slopy1/doa_24ghz_t/gnuradio_flowgraphs/aoa_estimation_bladerf.pdf

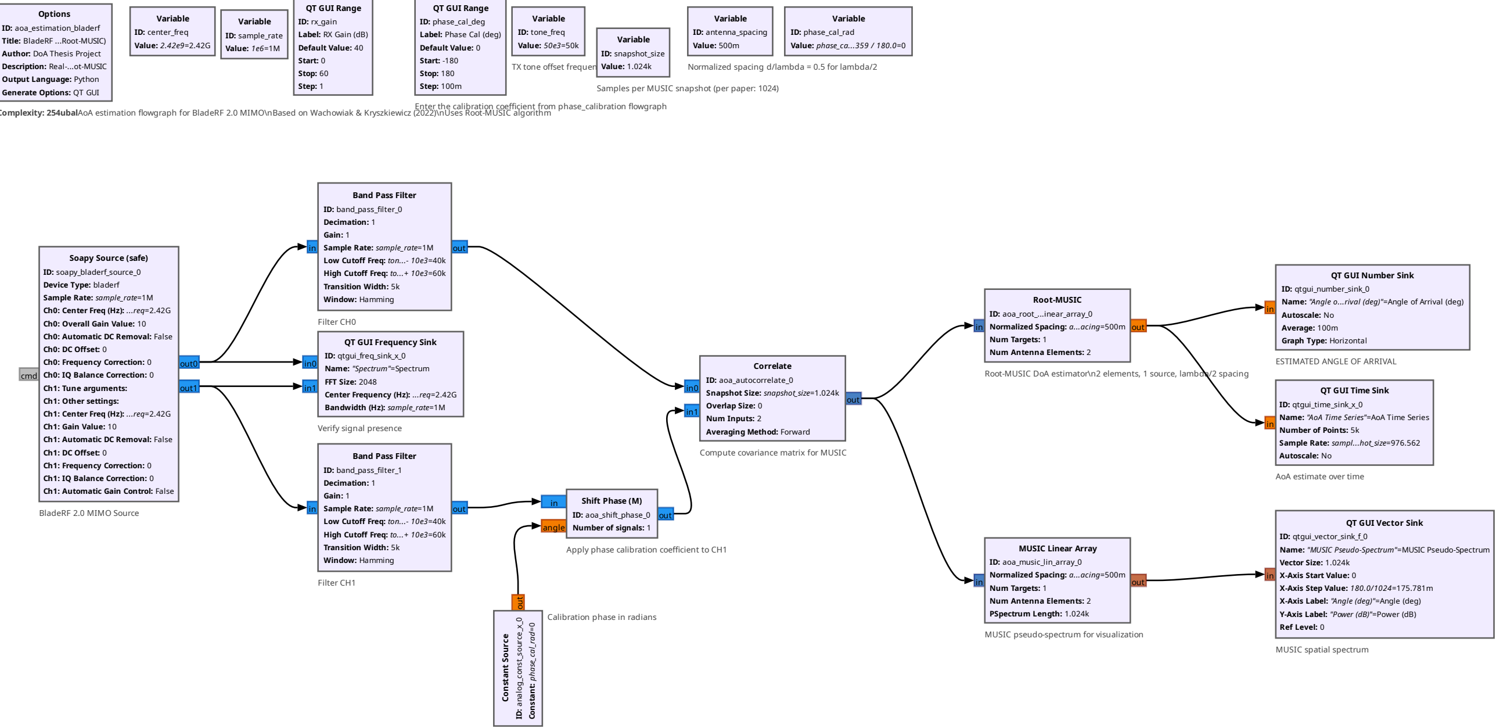
[picture p1: figure]
TX tone offset frequency; Calibration phase in radians; Compute covariance matrix for MUSIC; MUSIC pseudo-spectrum for visualization; Filter CH0; Filter CH1; Verify signal presence; ESTIMATED ANGLE OF ARRIVAL; AoA estimate over time; MUSIC spatial spectrum; BladeRF 2.0 MIMO Source; Options ID: aoa_estimation_bladerf Title: BladeRF ...Root-MUSIC) Author: DoA Thesis Project Description: Real-...ot-MUSIC Output Language: Python Generate Options: QT GUI; Variable ID: antenna_spacing Value: 500m; Variable ID: center_freq Value: 2.42e9=2.42G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

Complexity: 254ubalAoA estimation flowgraph for BladeRF 2.0 MIMO\nBased on Wachowiak & Kryszkiewicz (2022)\nUses Root-MUSIC algorithm

Normalized spacing d/lambda = 0.5 for lambda/2

Enter the calibration coefficient from phase_calibration flowgraph

Samples per MUSIC snapshot (per paper: 1024)

Root-MUSIC DoA estimator\n2 elements, 1 source, lambda/2 spacing

Apply phase calibration coefficient to CH1

Name: "Angle o...rival (deg)"=Angle of Arrival (deg)
