slopy1/doa_24ghz_t/results/spectrum_sweep_20260427_003050/spectrum_compare.png

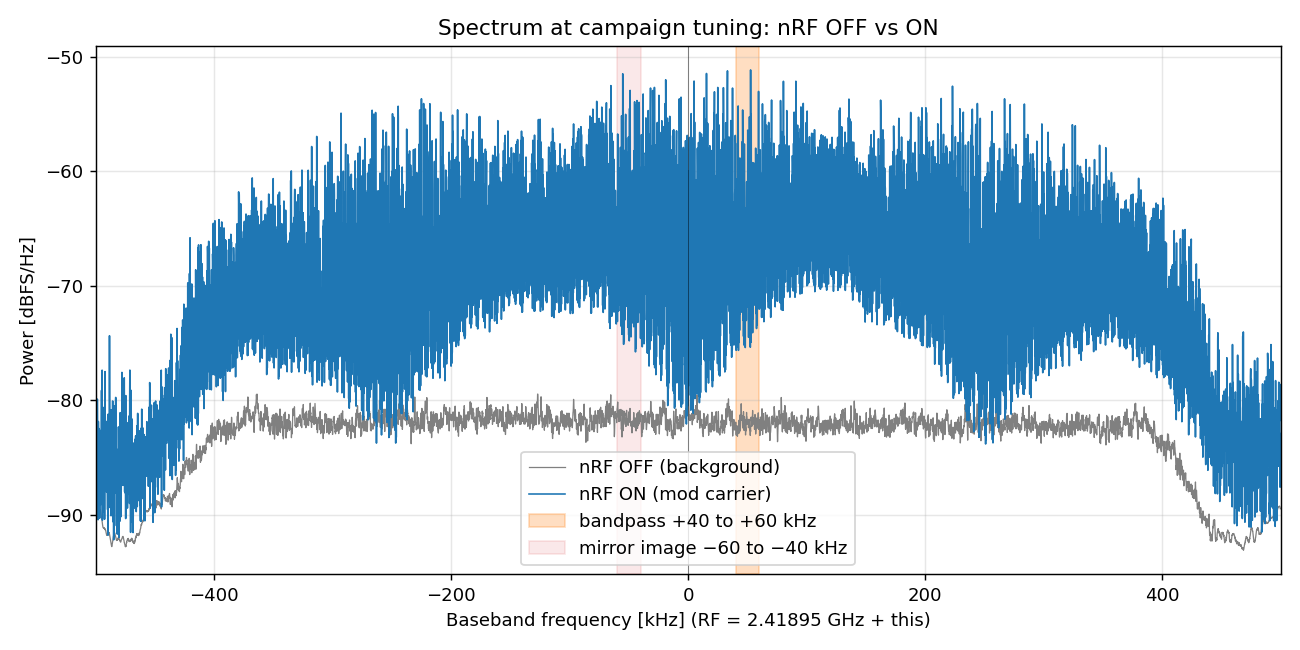
results/spectrum_sweep_20260427_003050/spectrum_compare.png
