slopy1/doa_24ghz_t/results/advisor_summary/arm_vs_fpga_delta.png

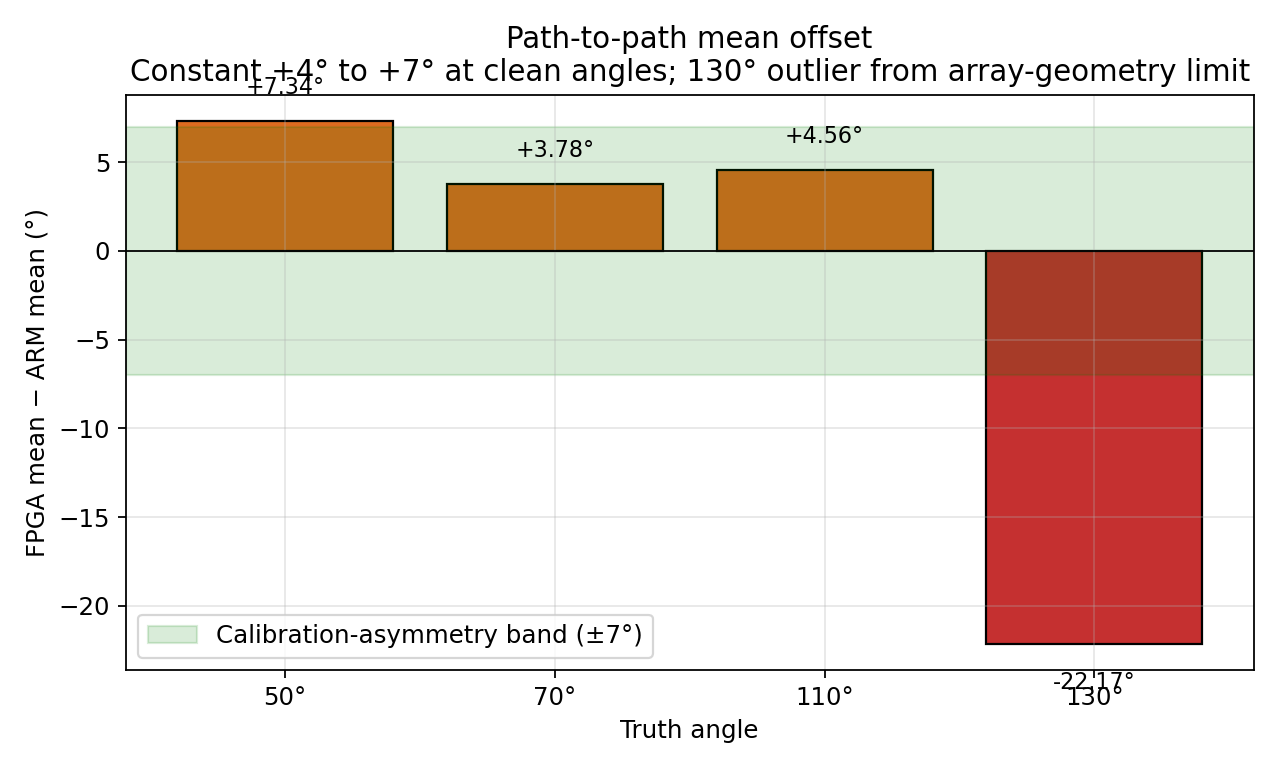
results/advisor_summary/arm_vs_fpga_delta.png
