slopy1/doa_24ghz_t/results/advisor_summary/arm_vs_fpga_per_angle.png

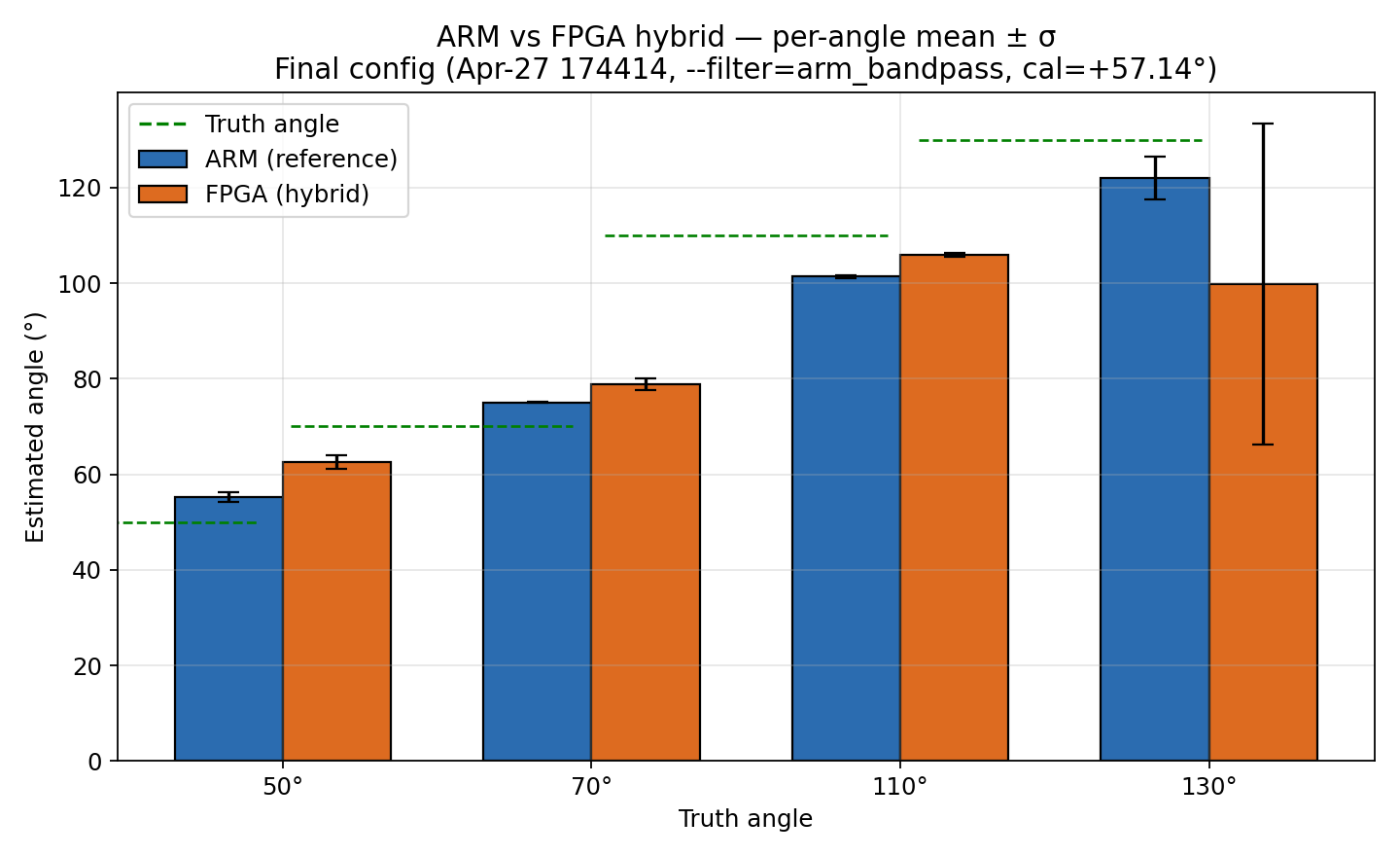
results/advisor_summary/arm_vs_fpga_per_angle.png
