slopy1/doa_24ghz_t/results/advisor_summary/broadside_anchor.png

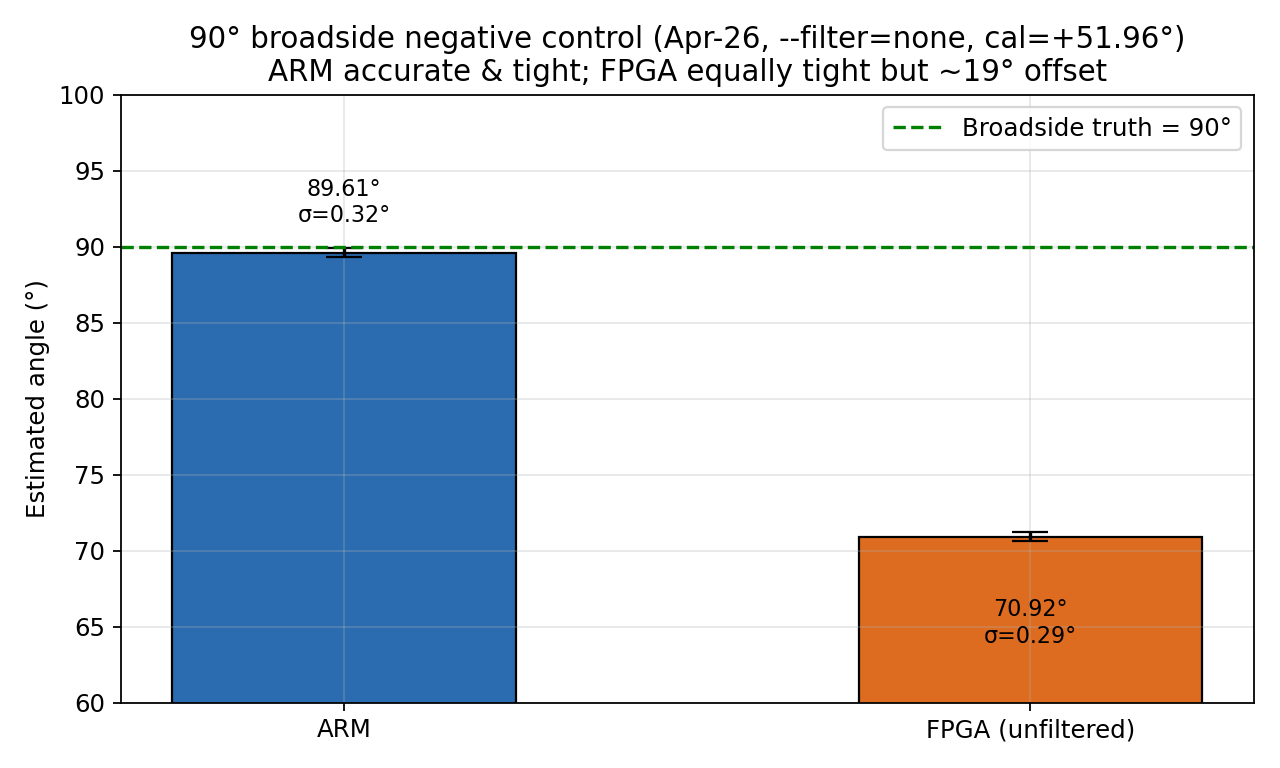
results/advisor_summary/broadside_anchor.png
