slopy1/doa_24ghz_t/results/advisor_summary/filter_regime_comparison.png

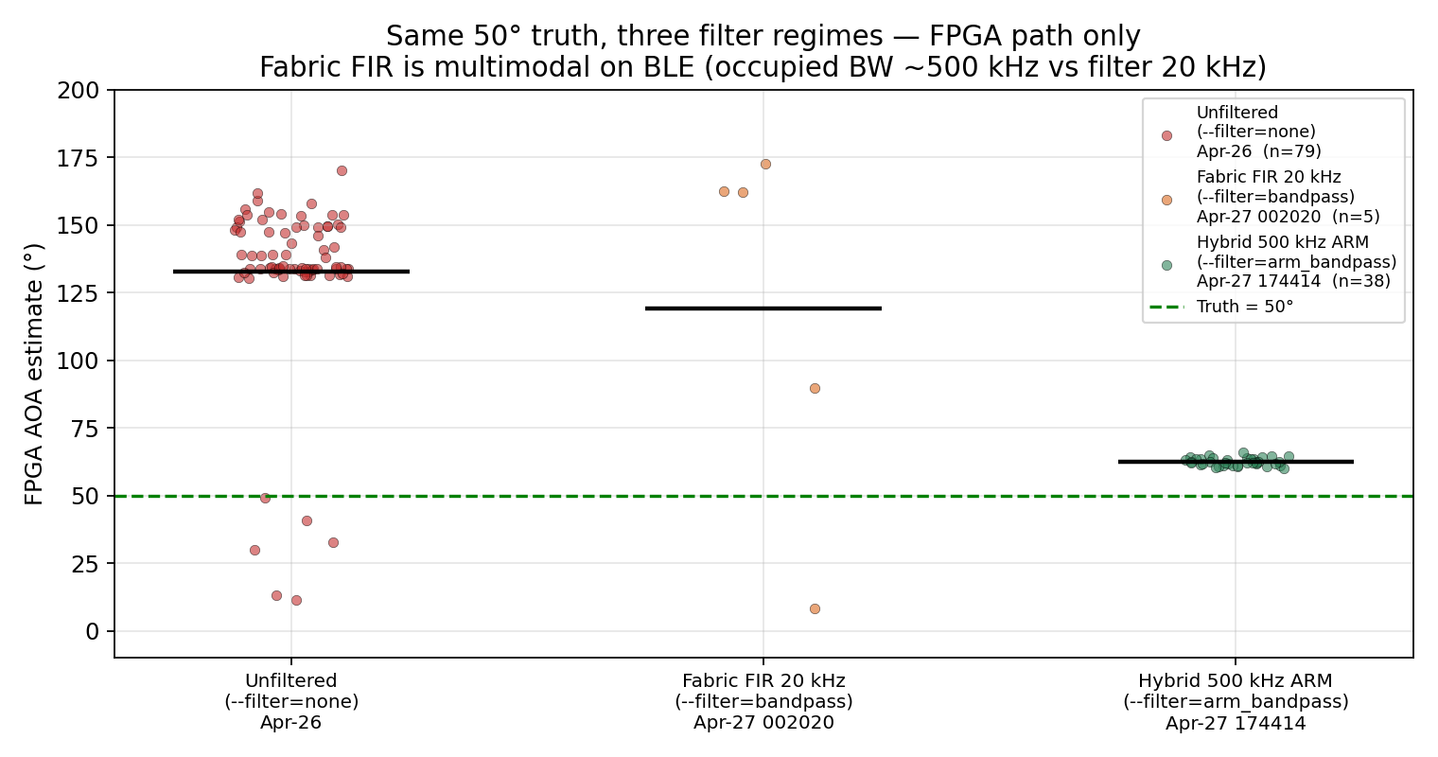
results/advisor_summary/filter_regime_comparison.png
