slopy1/doa_24ghz_t/results/advisor_summary/methodology_r2.png

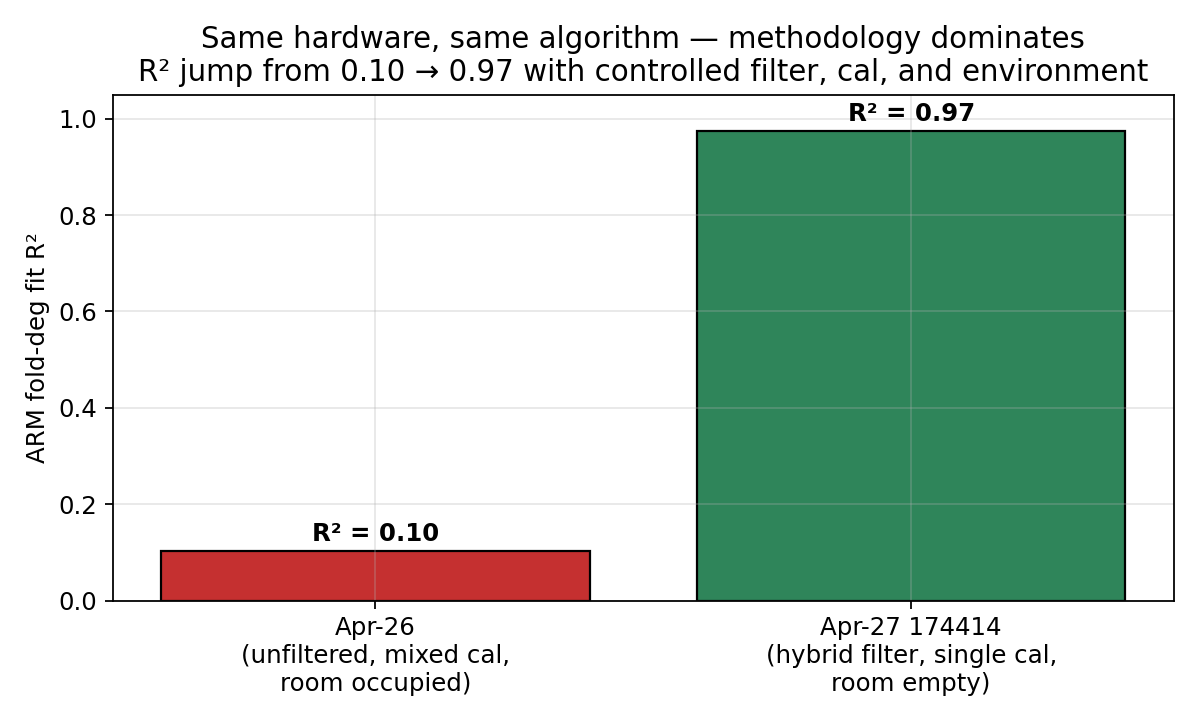
results/advisor_summary/methodology_r2.png
