slopy1/doa_24ghz_t/results/arm_vs_fpga/hist_rootmusic_pair_90deg.png

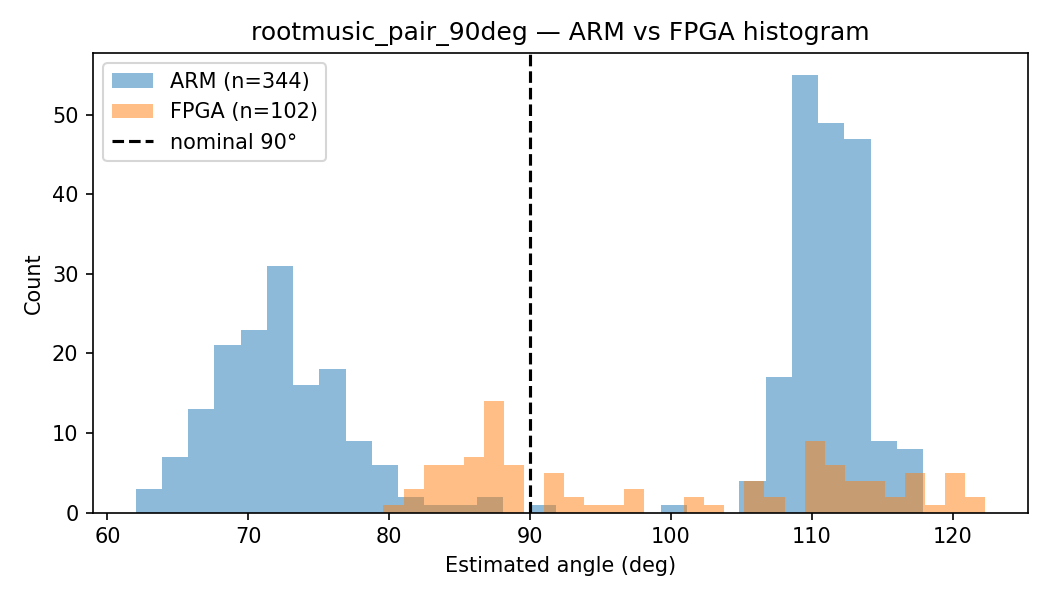
results/arm_vs_fpga/hist_rootmusic_pair_90deg.png
