slopy1/doa_24ghz_t/results/arm_vs_fpga/multi_algo_summary.png

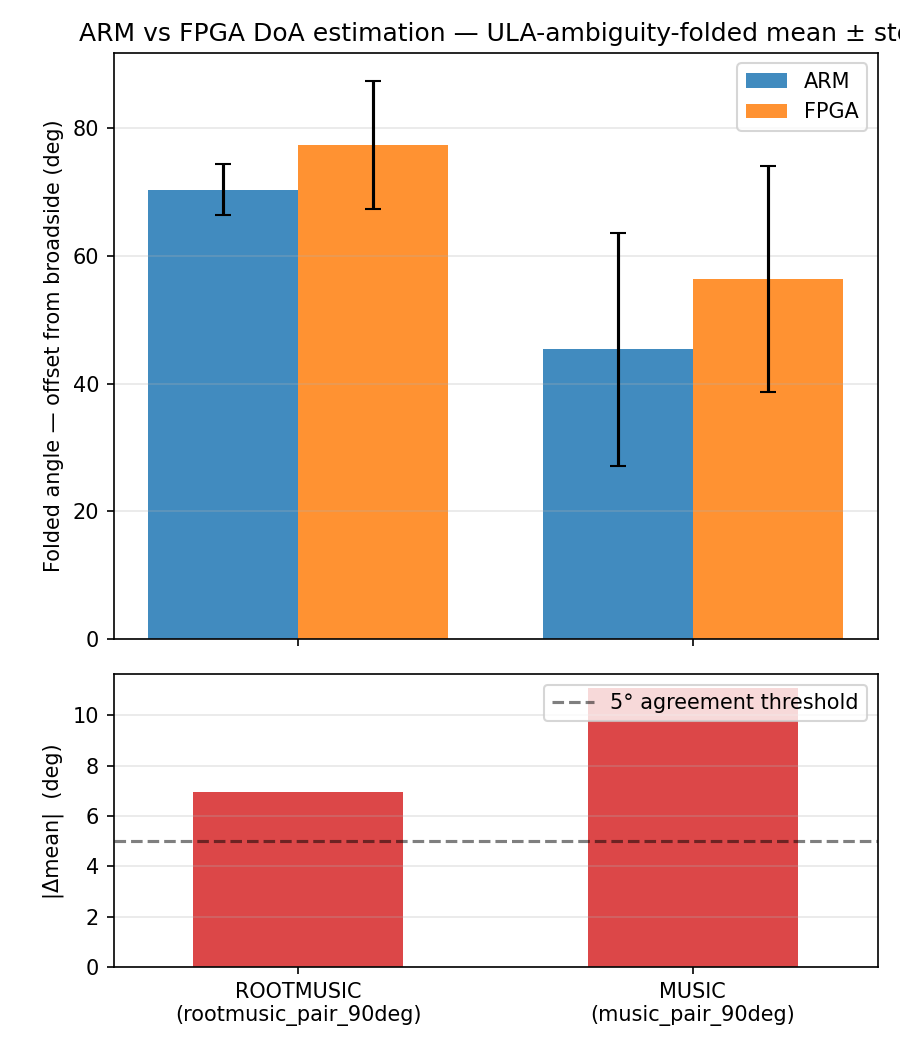
results/arm_vs_fpga/multi_algo_summary.png
