slopy1/doa_24ghz_t/results/arm_vs_fpga/timeseries_music_pair_90deg.png

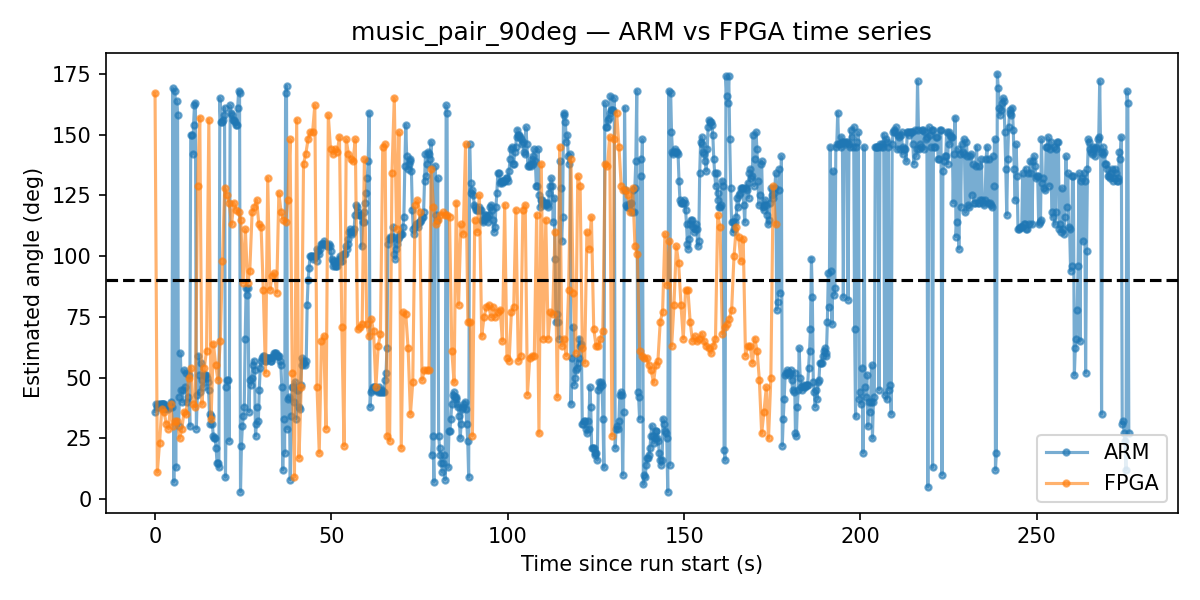
results/arm_vs_fpga/timeseries_music_pair_90deg.png
