slopy1/doa_24ghz_t/results/campaign_20260426/folded_measured_vs_truth.png

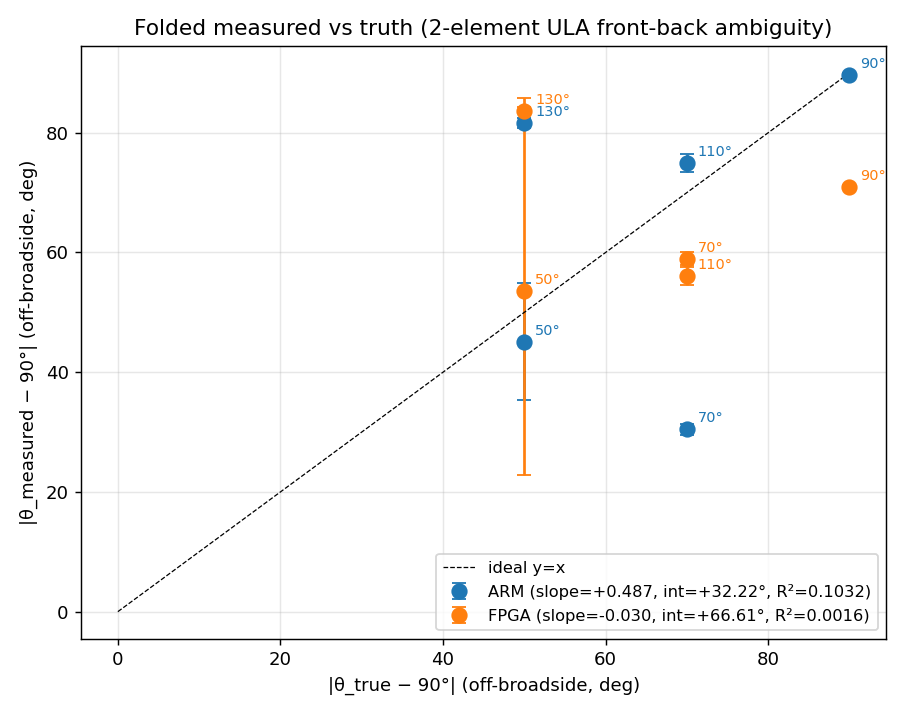
results/campaign_20260426/folded_measured_vs_truth.png
