slopy1/doa_24ghz_t/results/campaign_20260426/measured_vs_truth_deg.png

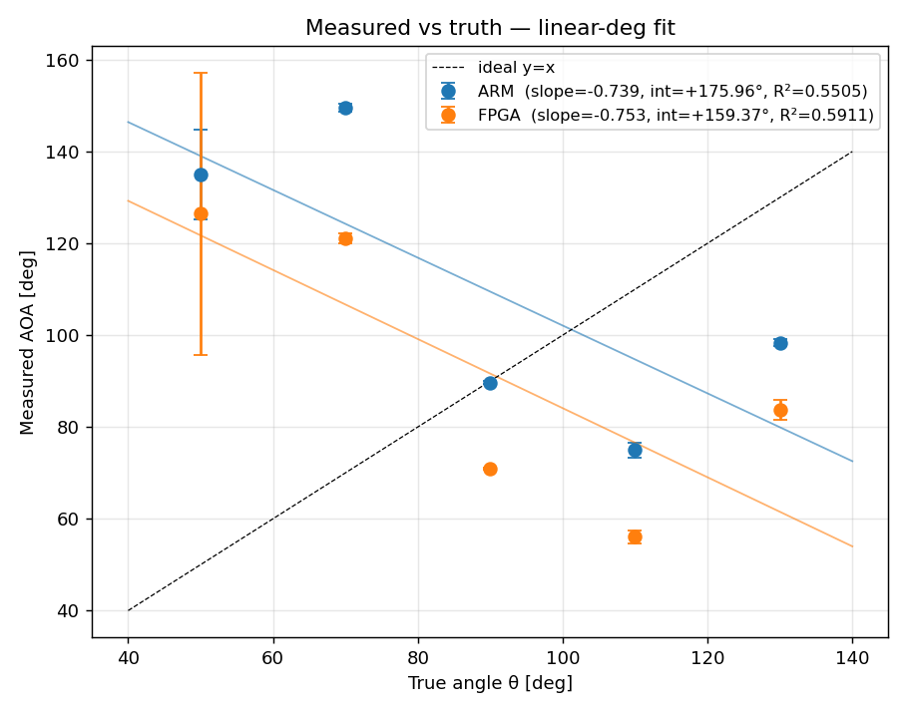
results/campaign_20260426/measured_vs_truth_deg.png
