slopy1/doa_24ghz_t/results/campaign_20260427_174414/folded_measured_vs_truth.png

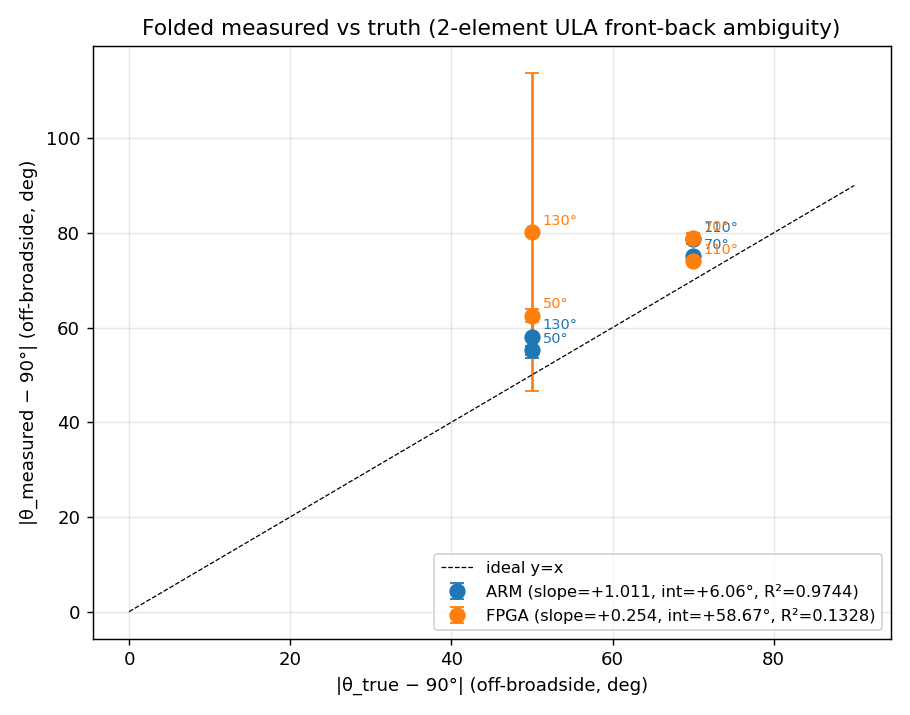
results/campaign_20260427_174414/folded_measured_vs_truth.png
