slopy1/doa_24ghz_t/results/campaign_20260427_174414/time_series_per_angle.png

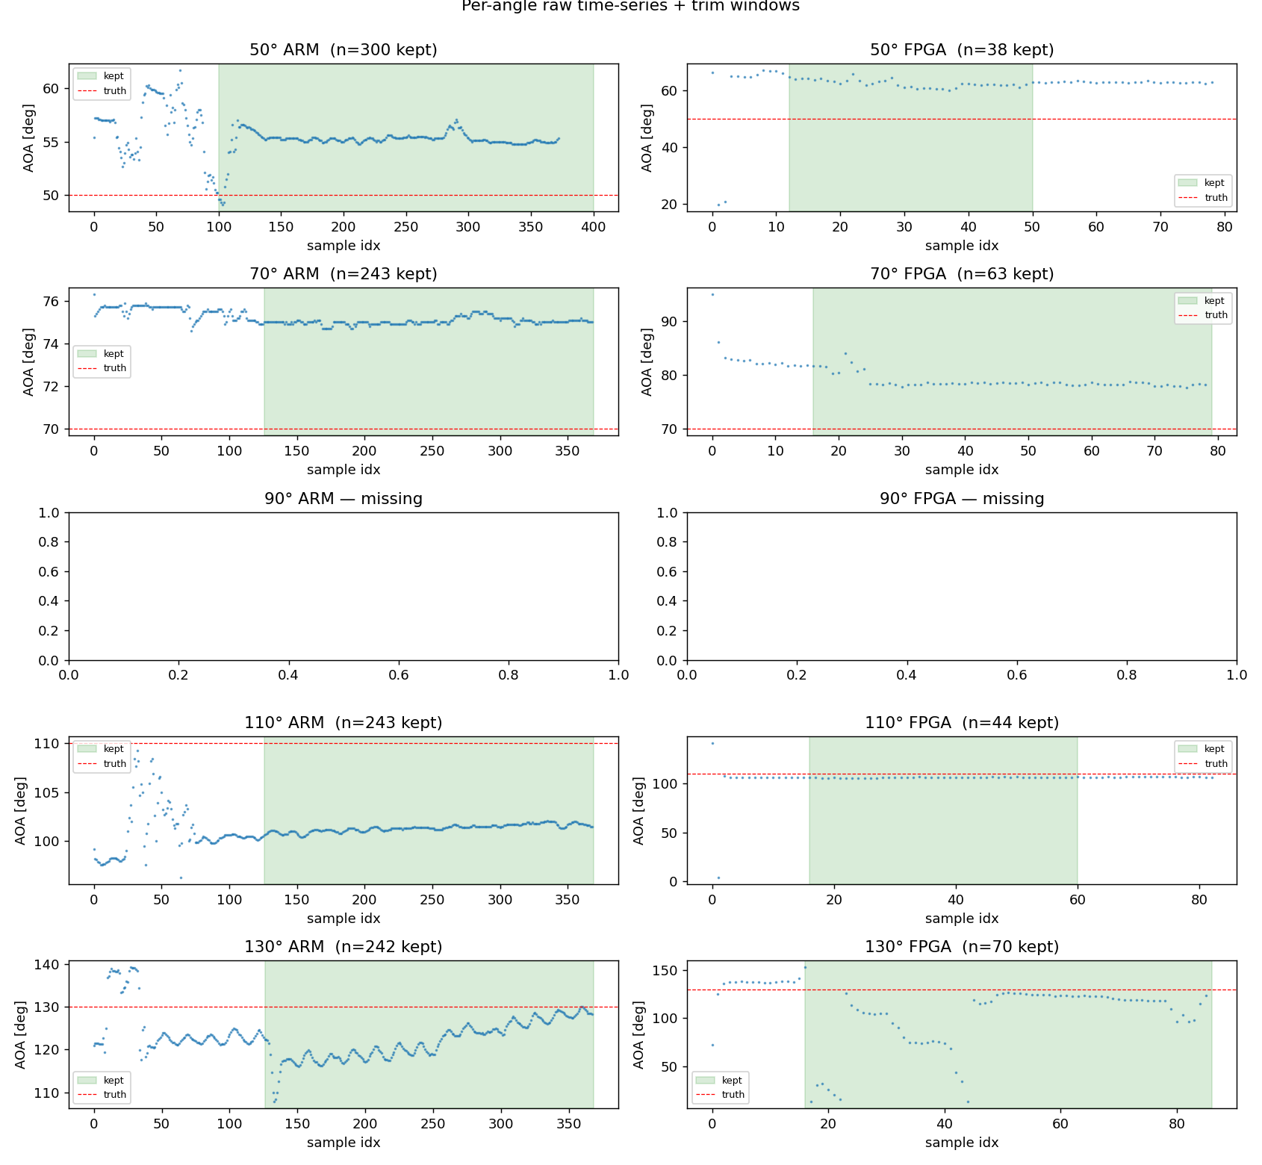
results/campaign_20260427_174414/time_series_per_angle.png
