slopy1/doa_24ghz_t/results/campaign_20260429_203028_v2/arm_minus_fpga_delta.png

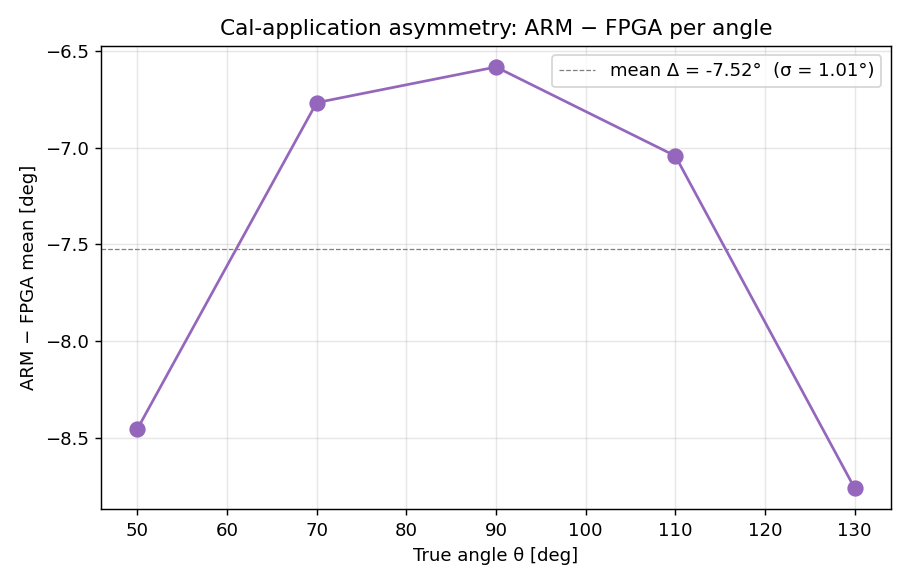
results/campaign_20260429_203028_v2/arm_minus_fpga_delta.png
