slopy1/doa_24ghz_t/results/campaign_20260429_203028_v2/folded_measured_vs_truth.png

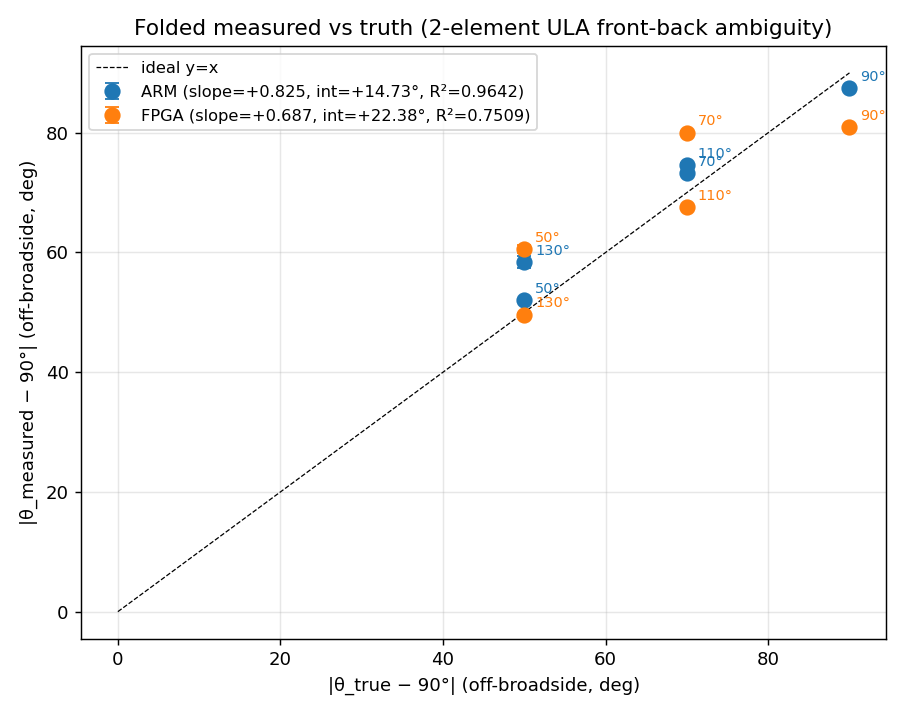
results/campaign_20260429_203028_v2/folded_measured_vs_truth.png
