slopy1/doa_24ghz_t/results/campaign_20260429_203028_v2/time_series_per_angle.png

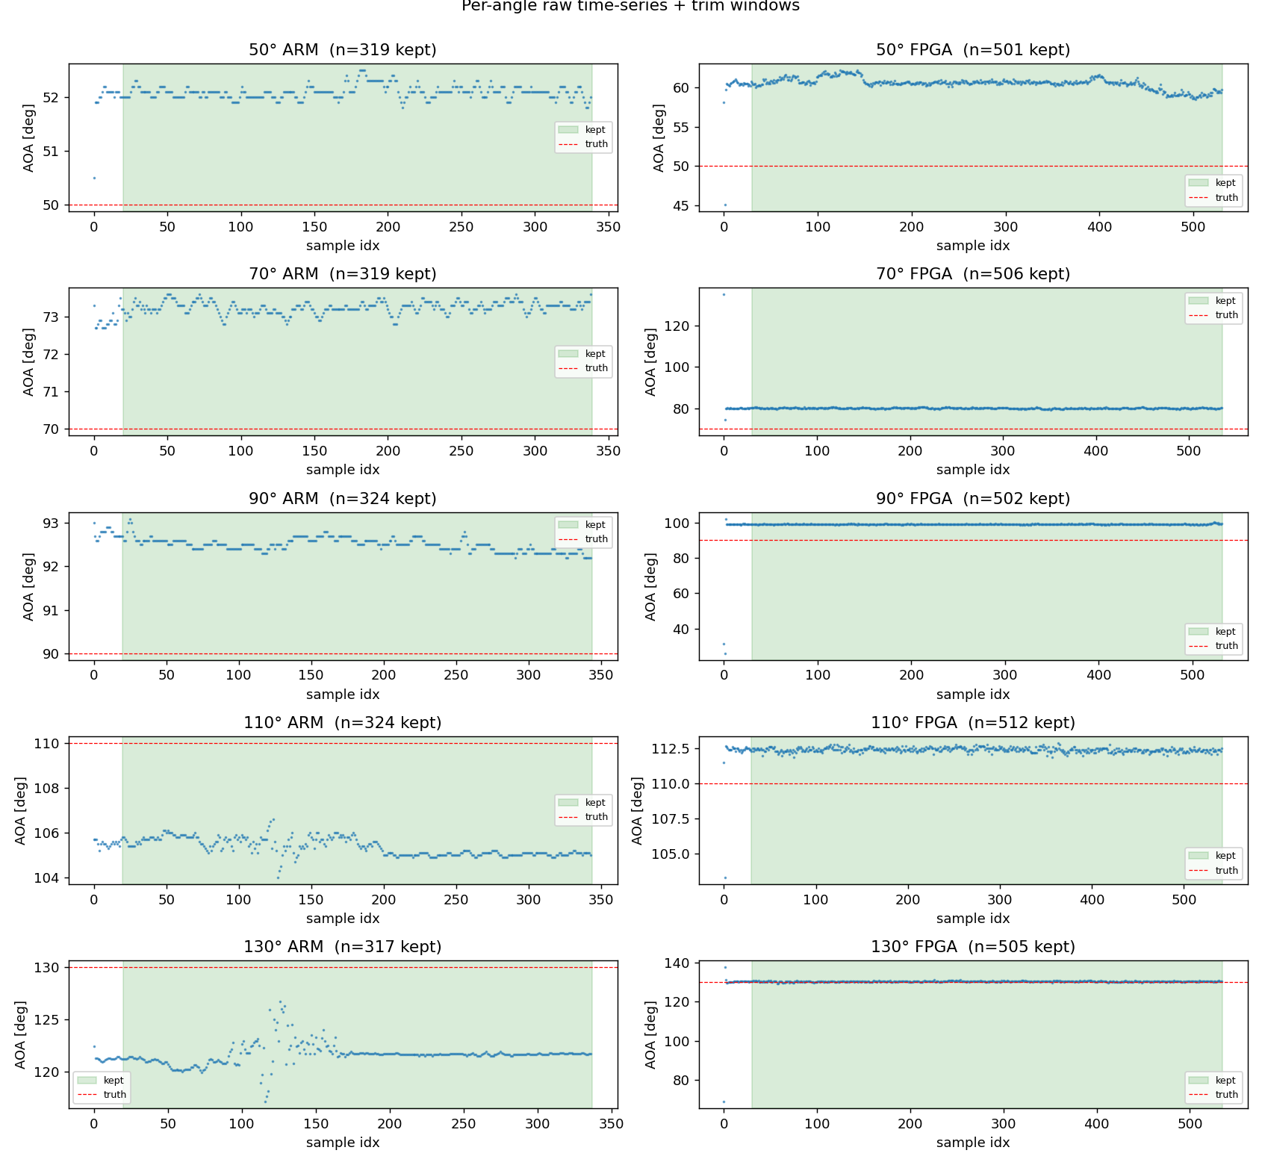
results/campaign_20260429_203028_v2/time_series_per_angle.png
