slopy1/doa_24ghz_t/results/quicklook/aoa_smoketest_ARM_ROOTMUSIC_20180309_175110.png

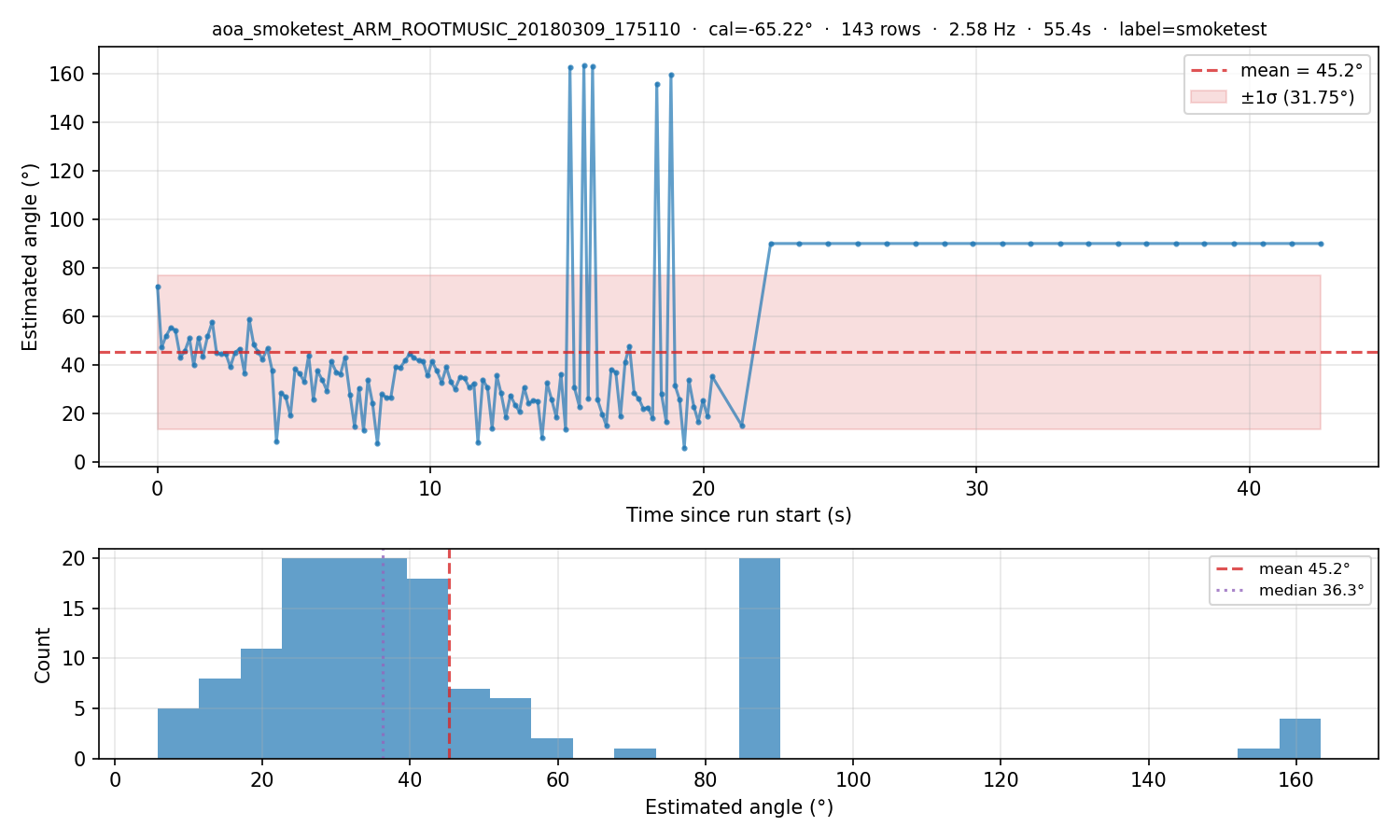
results/quicklook/aoa_smoketest_ARM_ROOTMUSIC_20180309_175110.png
