slopy1/doa_24ghz_t/results/quicklook/aoa_smoketest_ARM_ROOTMUSIC_20260405_044839.png

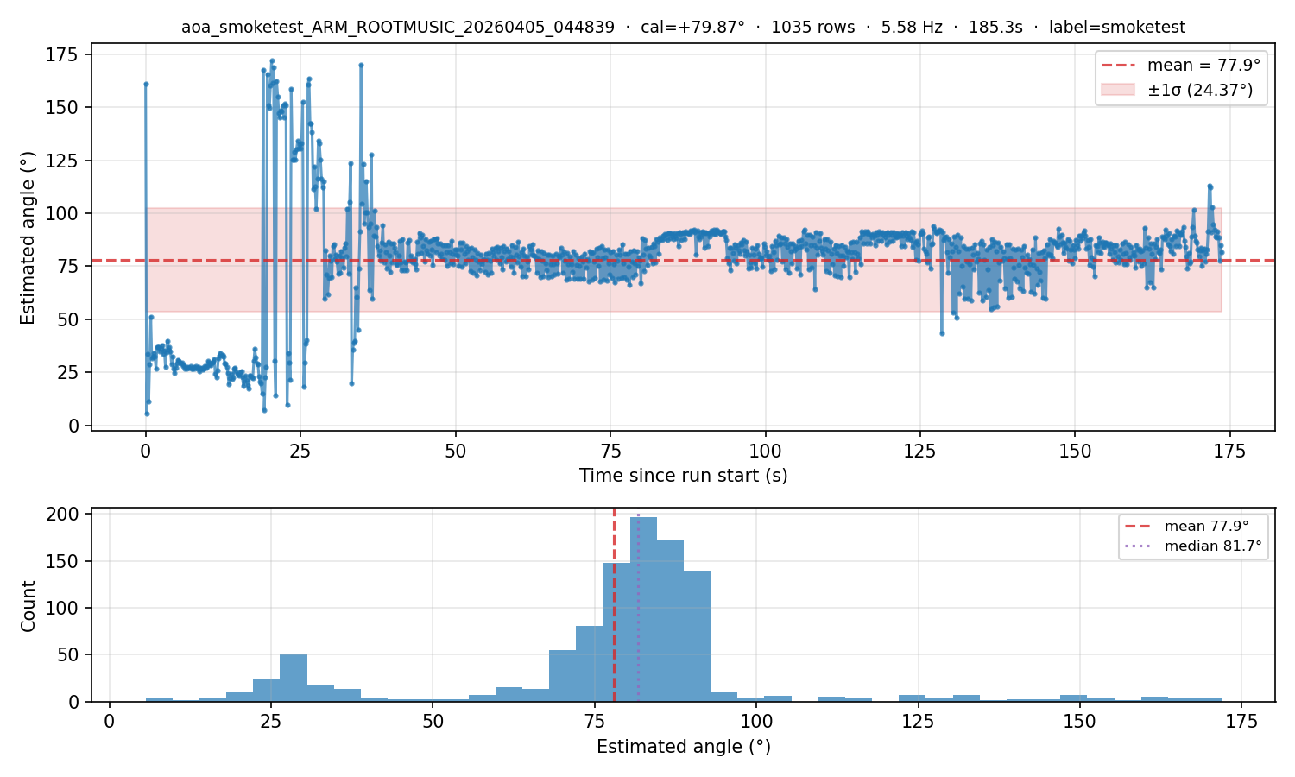
results/quicklook/aoa_smoketest_ARM_ROOTMUSIC_20260405_044839.png
