slopy1/doa_24ghz_t/results/quicklook/overlay.png

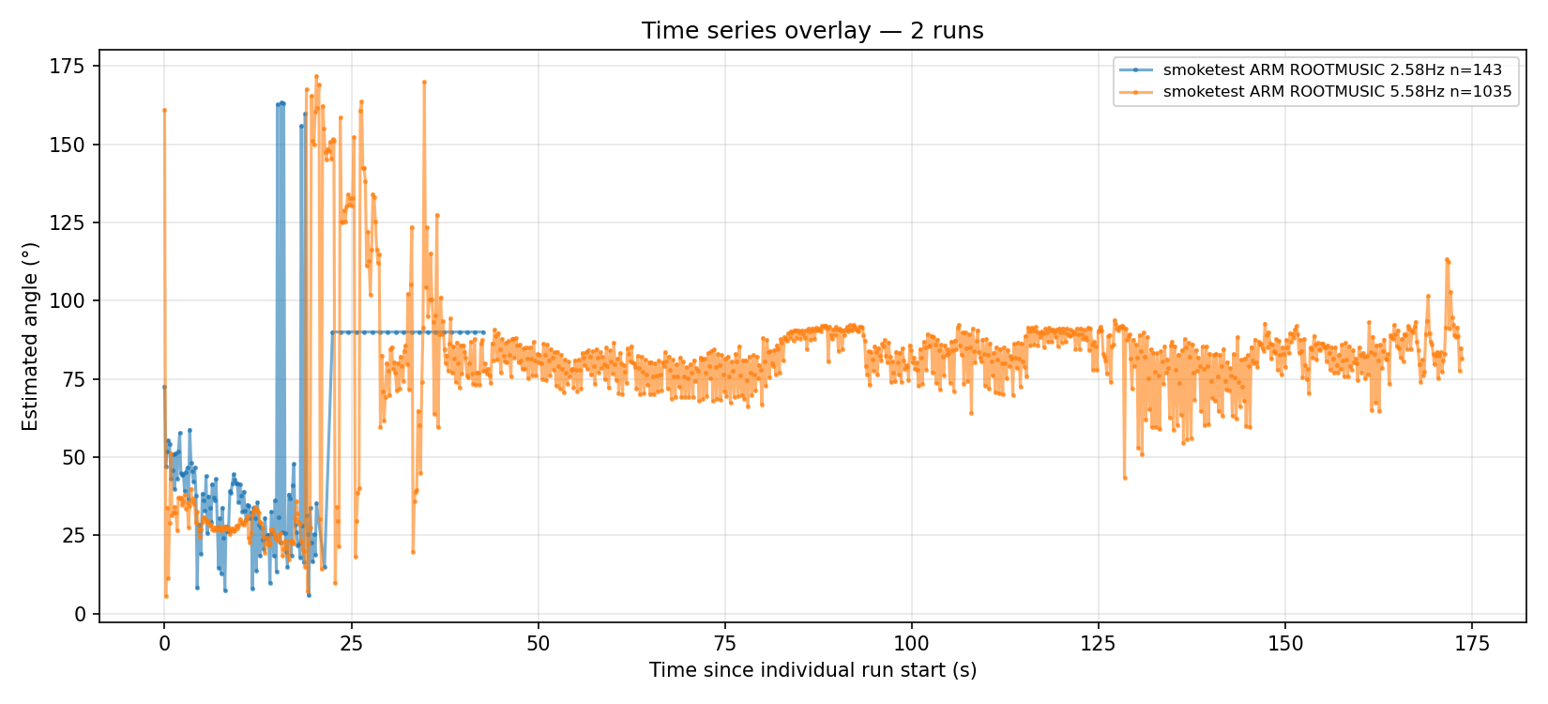
results/quicklook/overlay.png
